CIRCUITSTATE/Mitayi-Pico-RP2040/Export/R0.6/2025-04-27/Renders/Mitayi-Pico-D1-R0.6-PCB-Left-27042025-1.png

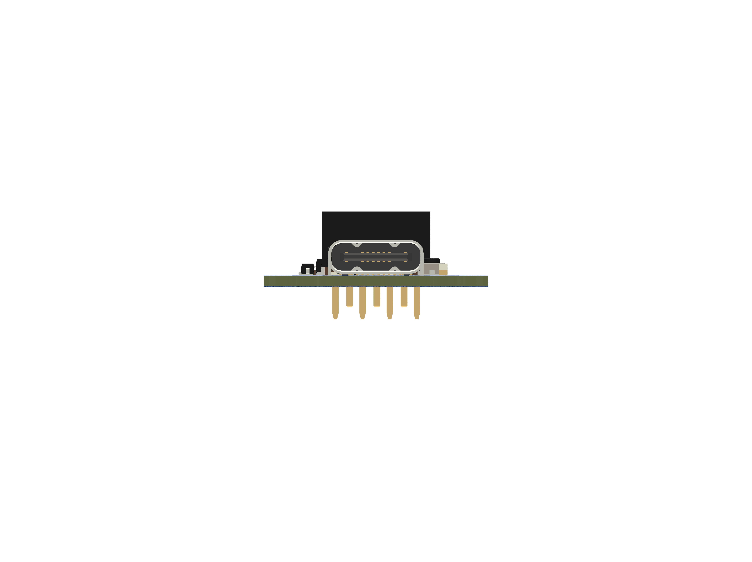
Export/R0.6/2025-04-27/Renders/Mitayi-Pico-D1-R0.6-PCB-Left-27042025-1.png
