CIRCUITSTATE/Mitayi-Pico-RP2040/Revisions/Mitayi-Pico-RP2040-r0.3/Production/PCBWay/[1] 26-08-2022/Mitayi-Pico-RP2040-PCBWay-Order-Details-01.png

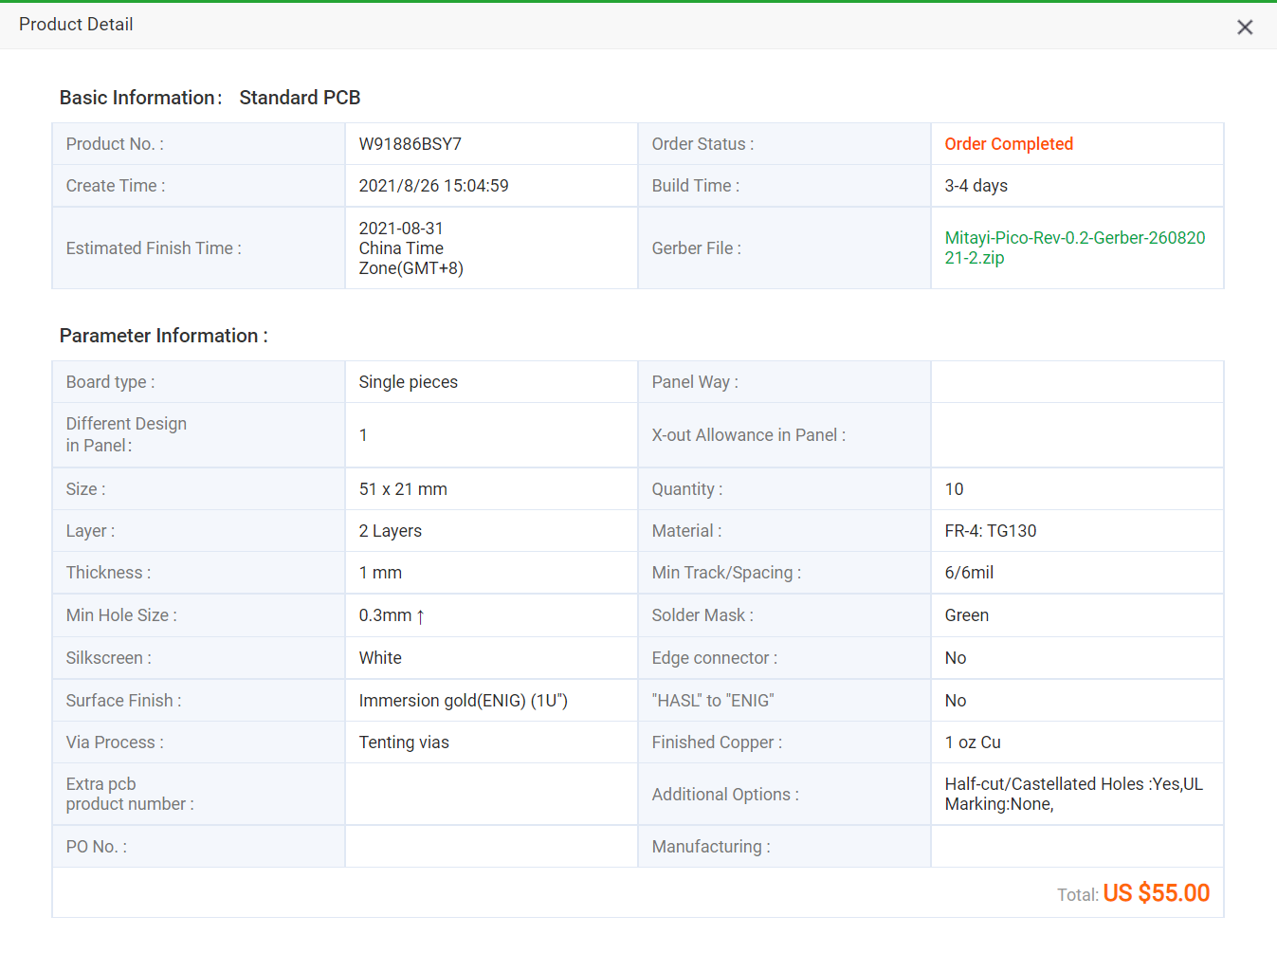
Revisions/Mitayi-Pico-RP2040-r0.3/Production/PCBWay/[1] 26-08-2022/Mitayi-Pico-RP2040-PCBWay-Order-Details-01.png
