CIRCUITSTATE/Mitayi-Pico-RP2040/Revisions/Mitayi-Pico-RP2040-r0.5/Revisions/Mitayi-Pico-RP2040-r0.2/Export/[3] 24-11-2021/Assembly/Mitayi-Pico-RP2040-v0.2-Assembly-Drawing-01_1.png

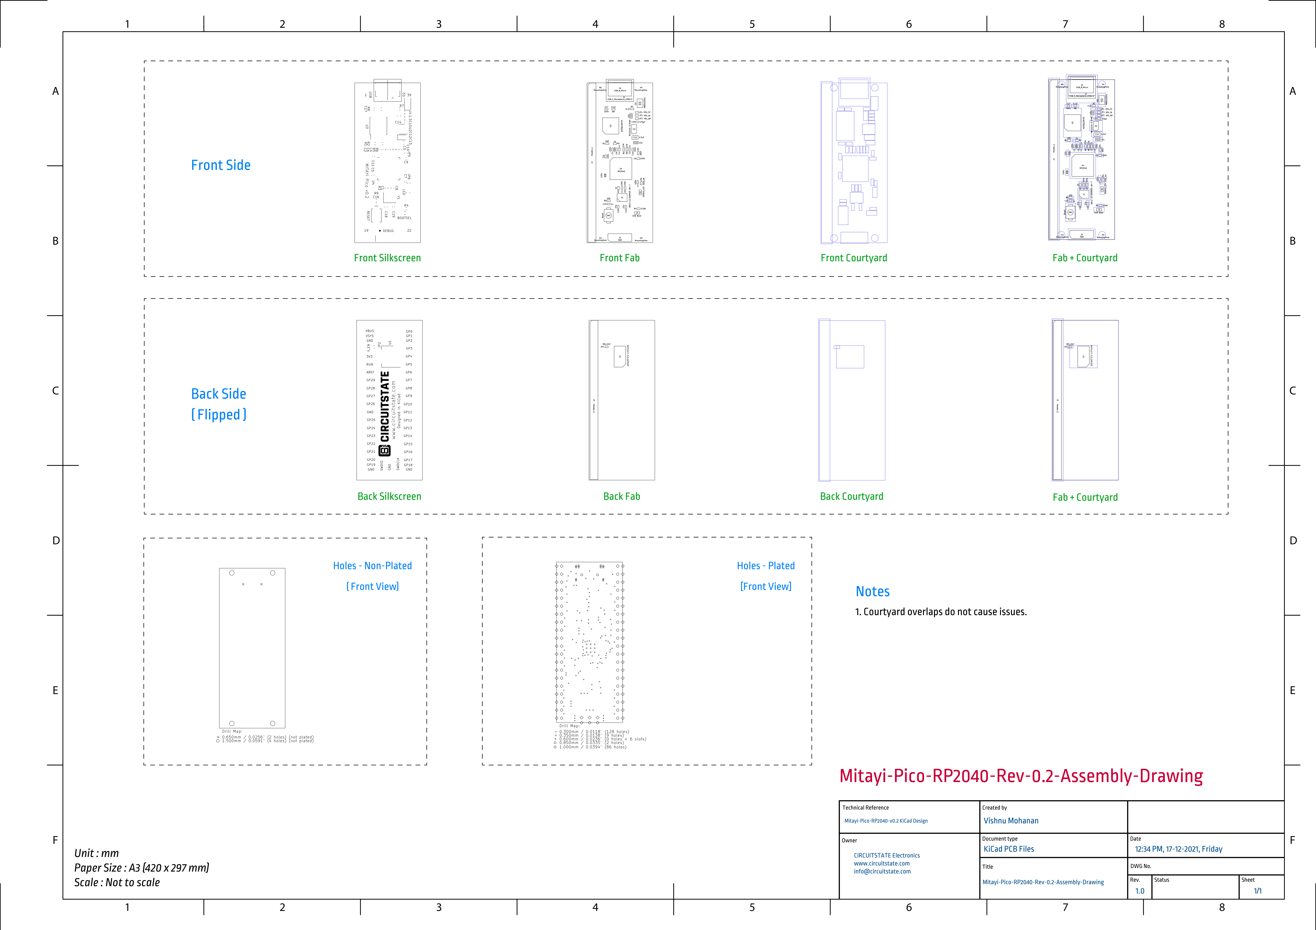
Revisions/Mitayi-Pico-RP2040-r0.5/Revisions/Mitayi-Pico-RP2040-r0.2/Export/[3] 24-11-2021/Assembly/Mitayi-Pico-RP2040-v0.2-Assembly-Drawing-01_1.png
