CIRCUITSTATE/Mitayi-Pico-RP2040/Revisions/Mitayi-Pico-RP2040-r0.4/Export/[6] 23-09-2022/r0.4/Images/Mitayi Pico - PCB.0.4.B.png

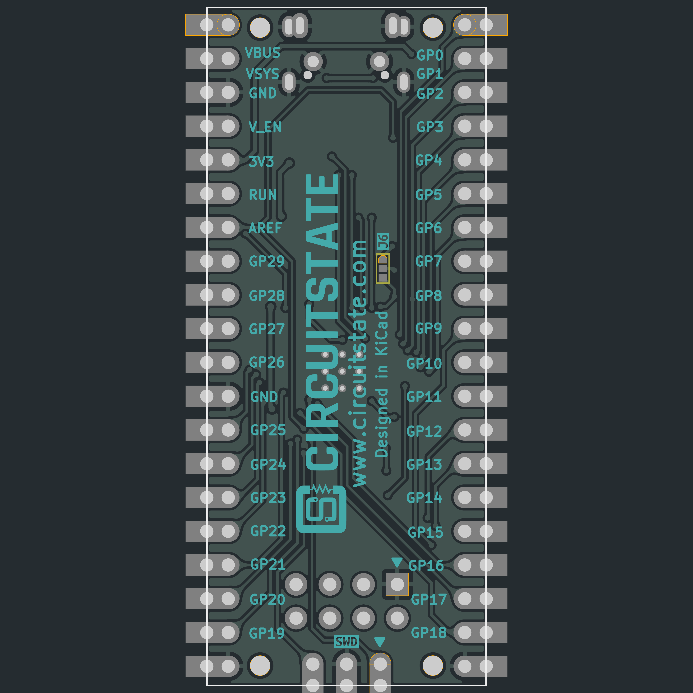
Revisions/Mitayi-Pico-RP2040-r0.4/Export/[6] 23-09-2022/r0.4/Images/Mitayi Pico - PCB.0.4.B.png
