CIRCUITSTATE/Mitayi-Pico-RP2040/Revisions/Mitayi-Pico-RP2040-r0.4/Export/[6] 23-09-2022/r0.4/Images/Mitayi-Pico-RP2040-r0.4-PCB-01-Front-2.png

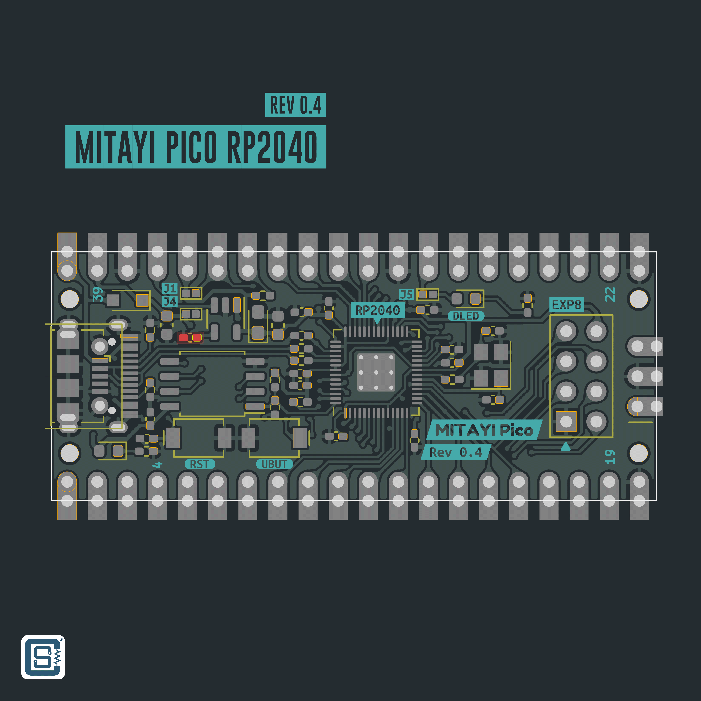
Revisions/Mitayi-Pico-RP2040-r0.4/Export/[6] 23-09-2022/r0.4/Images/Mitayi-Pico-RP2040-r0.4-PCB-01-Front-2.png
