CIRCUITSTATE/Mitayi-Pico-RP2040/Revisions/Mitayi-Pico-RP2040-r0.5/Revisions/Mitayi-Pico-RP2040-r0.2/Export/[3] 24-11-2021/PCB/Mitayi-Pico-RP2040-B_Courtyard.pdf

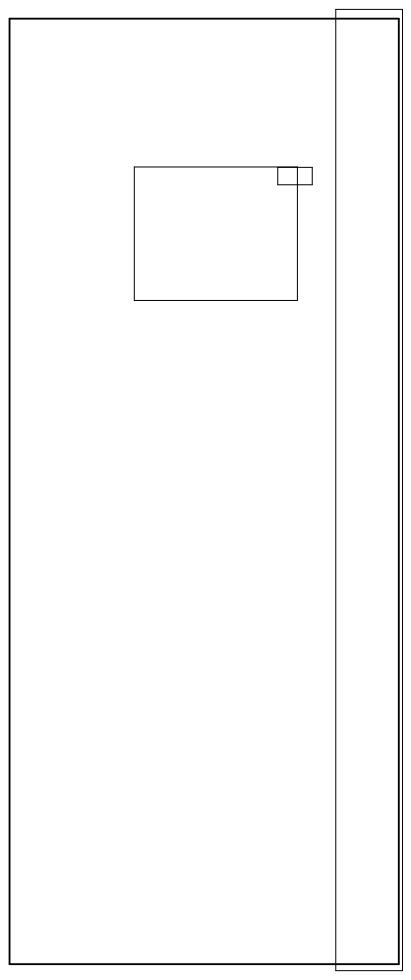
[picture p23: page 1]

Copyright 2021 CIRCUITSTATE Electronics
File: Mitayi-Pico-RP2040.kicad_pcb Sheet: CIRCUITSTATE Electronics Designed by Vishnu Mohanan

Id: 1/1 Title: Mitayi Pico - PCB
