CIRCUITSTATE/Mitayi-Pico-RP2040/Revisions/Mitayi-Pico-RP2040-r0.5/Revisions/Mitayi-Pico-RP2040-r0.2/Export/[3] 24-11-2021/Assembly/Mitayi-Pico-RP2040-v0.2-Assembly-Drawing-01.pdf

## Front Side

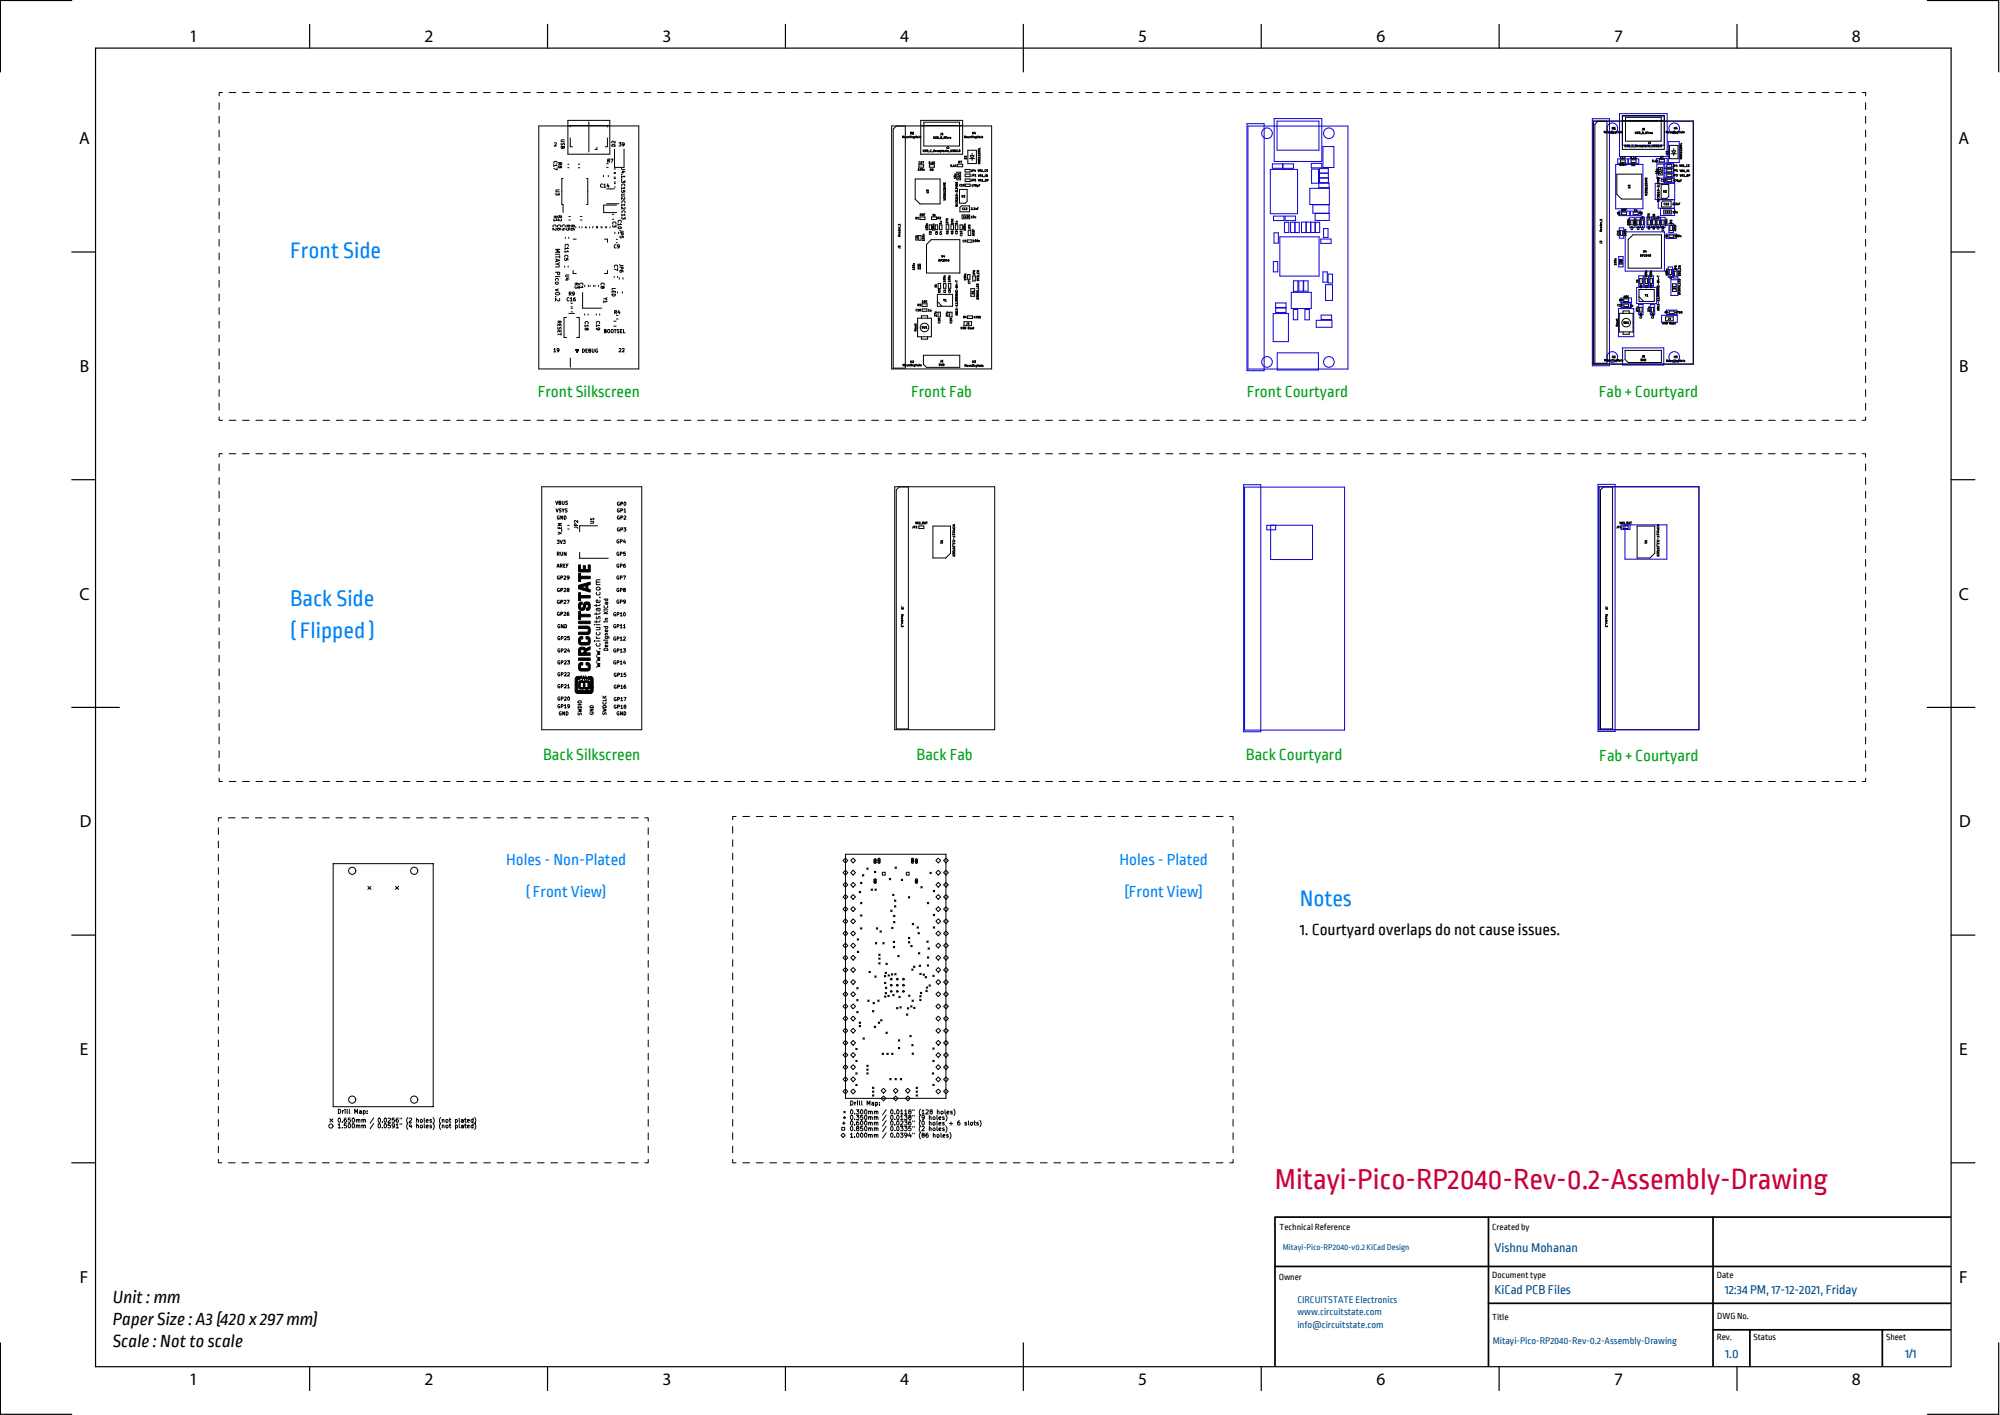
[picture p24: page 1]
Technical Reference; Owner; Created by; Document type; Date; Mitayi-Pico-RP2040-v0.2 KiCad Design; Vishnu Mohanan; 12:34 PM, 17-12-2021, Friday; Front Silkscreen; Back Silkscreen; Holes - Plated; [Front View]; Notes; Back Fab; Back Courtyard; Front Fab; Front Courtyard; Fab + Courtyard; Back Side ( Flipped )

Holes - Non-Plated
( Front View)

1. Courtyard overlaps do not cause issues.

Mitayi-Pico-RP2040-Rev-0.2-Assembly-Drawing

Unit : mm
Paper Size : A3 (420 x 297 mm)
Scale : Not to scale

KiCad PCB Files

CIRCUITSTATE Electronics
www.circuitstate.com
info@circuitstate.com

Title Mitayi-Pico-RP2040-Rev-0.2-Assembly-Drawing | DWG No.

Rev. 1.0 | Status | Sheet 1/1
