CIRCUITSTATE/Mitayi-Pico-RP2040/Export/R0.6/2025-04-27/PCB/Mitayi-Pico-D1-R0.6-Edge_Cuts.pdf

Id: 1/1 Title: Mitayi-Pico-D1
