CIRCUITSTATE/Mitayi-Pico-RP2040/Export/R0.6/2025-04-27/PCB/Mitayi-Pico-D1-R0.6-F_Silkscreen.pdf

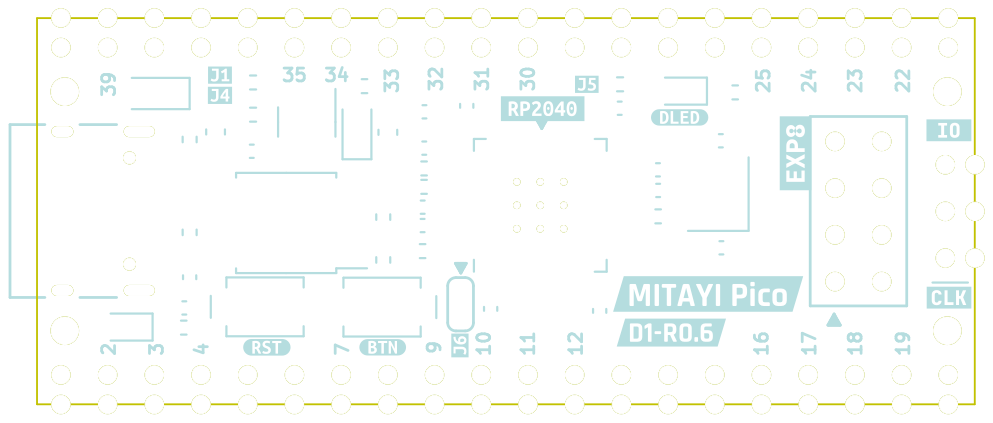
[picture p36: page 1]

Id: 1/1 Title: Mitayi-Pico-D1
