CIRCUITSTATE/Mitayi-Pico-RP2040/Export/R0.6/2025-04-27/PCB/Mitayi-Pico-D1-R0.6-PCB-PDF-All-27042025-1.pdf

D Date: 2025-04-27 KiCad; E.D.A. 9.0.1 Size: A4; Rev: 0.6; File: Mitayi-Pico-D1.kicad_pcb Sheet: CIRCUITSTATE; Electronics; LLP (www.circuitstate.com); Designed; by: Vishnu; Mohanan (@vishnumaiea) Released; under; MIT Open-source; License

Id: 1/1 Title: Mitayi-Pico-D1

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

Id: 1/1 Title: Mitayi-Pico-D1

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

Id: 1/1 Title: Mitayi-Pico-D1

D Date: 2025-04-27 KiCad; E.D.A. 9.0.1 Size: A4; Rev: 0.6; File: Mitayi-Pico-D1.kicad_pcb Sheet: CIRCUITSTATE; Electronics; LLP (www.circuitstate.com); Designed; by: Vishnu; Mohanan (@vishnumaiea) Released; under; MIT Open-source; License OSHW

Id: 1/1 Title: Mitayi-Pico-D1

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

Id: 1/1 Title: Mitayi-Pico-D1

D Date: 2025-04-27 KiCad; E.D.A. 9.0.1 Size: A4; Rev: 0.6; File: Mitayi-Pico-D1.kicad_pcb Sheet: CIRCUITSTATE; Electronics; LLP (www.circuitstate.com); Designed; by: Vishnu; Mohanan (@vishnumaiea) Released; under; MIT Open-source; License GP18 GP5 VSYS GND; GND; AREF; GP13 GP0 VBUS; www.circuitstate.com GP4; RUN; GP23 KiCad; with

Id: 1/1 Title: Mitayi-Pico-D1

Id: 1/1 Title: Mitayi-Pico-D1

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

Id: 1/1 Title: Mitayi-Pico-D1

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

Id: 1/1 Title: Mitayi-Pico-D1


Id: 1/1 Title: Mitayi-Pico-D1

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

Id: 1/1 Title: Mitayi-Pico-D1

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

Id: 1/1 Title: Mitayi-Pico-D1

D Date: 2025-04-27 KiCad; E.D.A. 9.0.1 Size: A4; Rev: 0.6; File: Mitayi-Pico-D1.kicad_pcb Sheet: CIRCUITSTATE; Electronics; LLP (www.circuitstate.com); Designed; by: Vishnu; Mohanan (@vishnumaiea) Released; under; MIT Open-source; License ²³³⁵

Id: 1/1 Title: Mitayi-Pico-D1

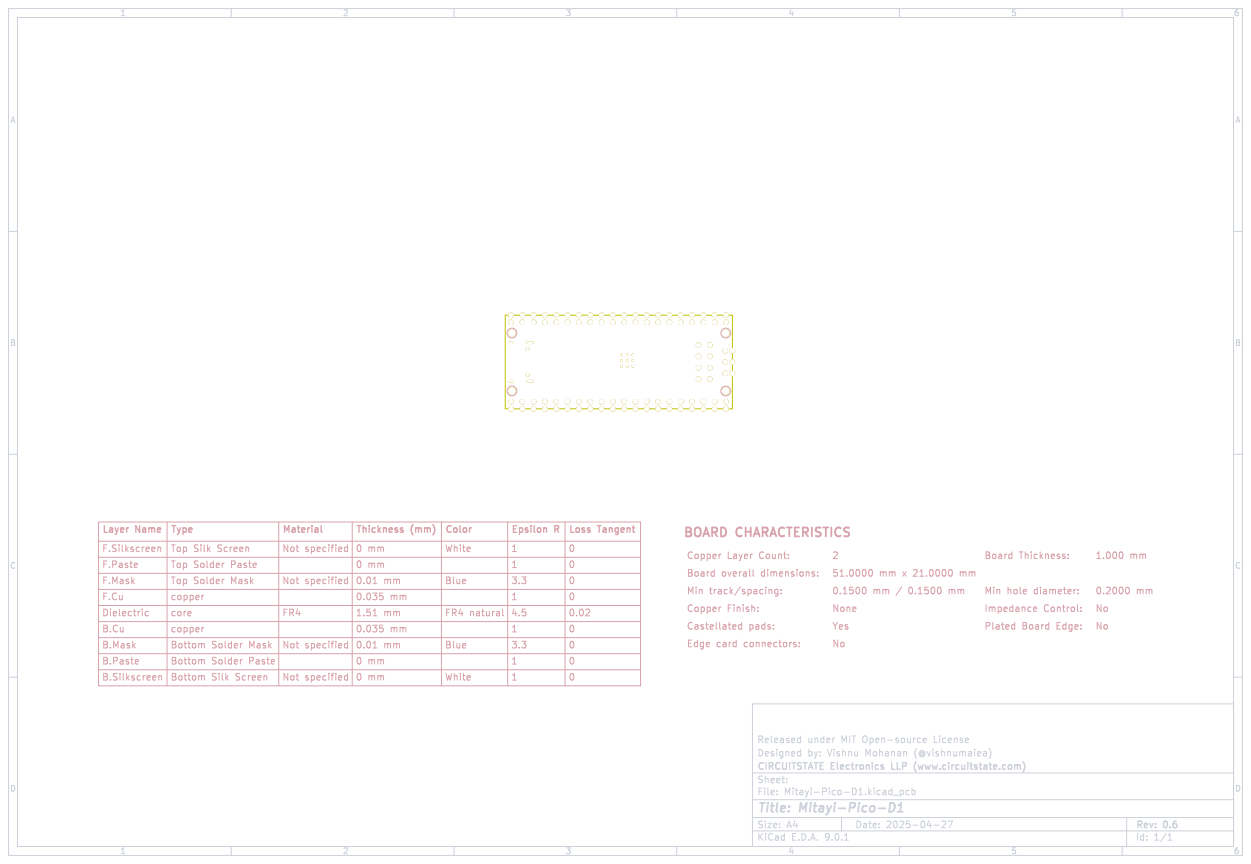
[picture p37: page 14]
D Date: 2025-04-27 KiCad; E.D.A. 9.0.1 Size: A4; Rev: 0.6; File: Mitayi-Pico-D1.kicad_pcb Sheet: CIRCUITSTATE; Electronics; LLP (www.circuitstate.com); Designed; by: Vishnu; Mohanan (@vishnumaiea) Released; under; MIT Open-source; License; 0.02 Top Solder; Paste B.Mask; Copper; Finish: Top Solder; Mask; No Not specified; Yes No; 0 F.Silkscreen; None; Min; hole diameter: 0.035 mm; Top Silk; Screen; Layer Name; Min track/spacing: 0 mm; Edge card; connectors:; Plated; Board; Edge: Dielectric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

F.Mask | | | 0 mm | Color 0 mm | 1

copper | Not specified | | Blue F.Paste | 1 | Loss Tangent 0 Type 0

Thickness (mm) | White

1 B.Silkscreen 3.3

Not specified | 0 mm | | 1 | 0

Id: 1/1 Title: Mitayi-Pico-D1

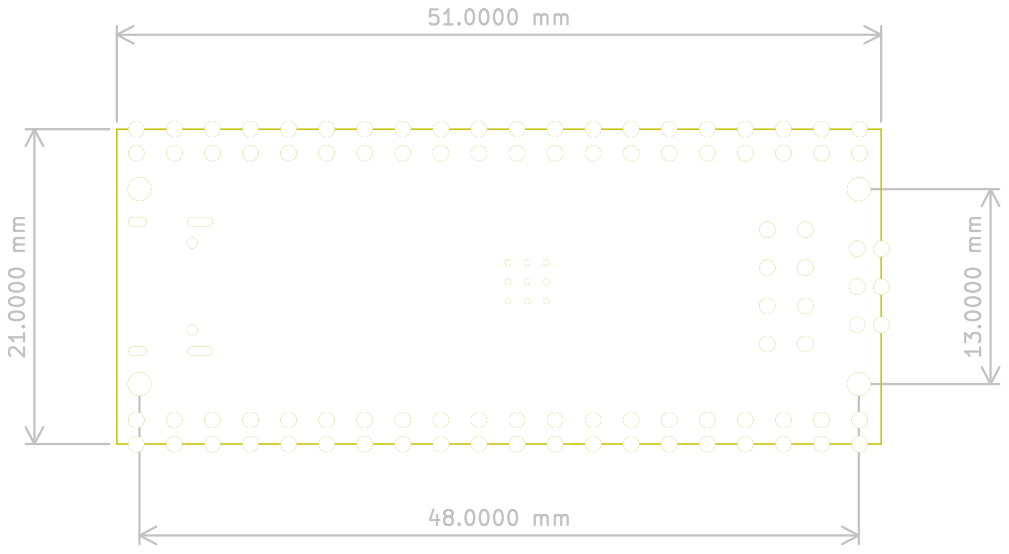
[picture p38: page 15]
D Date: 2025-04-27 KiCad; E.D.A. 9.0.1 Size: A4; Rev: 0.6; File: Mitayi-Pico-D1.kicad_pcb Sheet: CIRCUITSTATE; Electronics; LLP (www.circuitstate.com); Designed; by: Vishnu; Mohanan (@vishnumaiea) Released; under; MIT Open-source; License ¹³.0000 mm 21.0000 mm

Id: 1/1 Title: Mitayi-Pico-D1
