CIRCUITSTATE/Mitayi-Pico-RP2040/Export/R0.6/2025-04-27/SCH/Mitayi-Pico-D1-R0.6-SCH-27042025-1.pdf

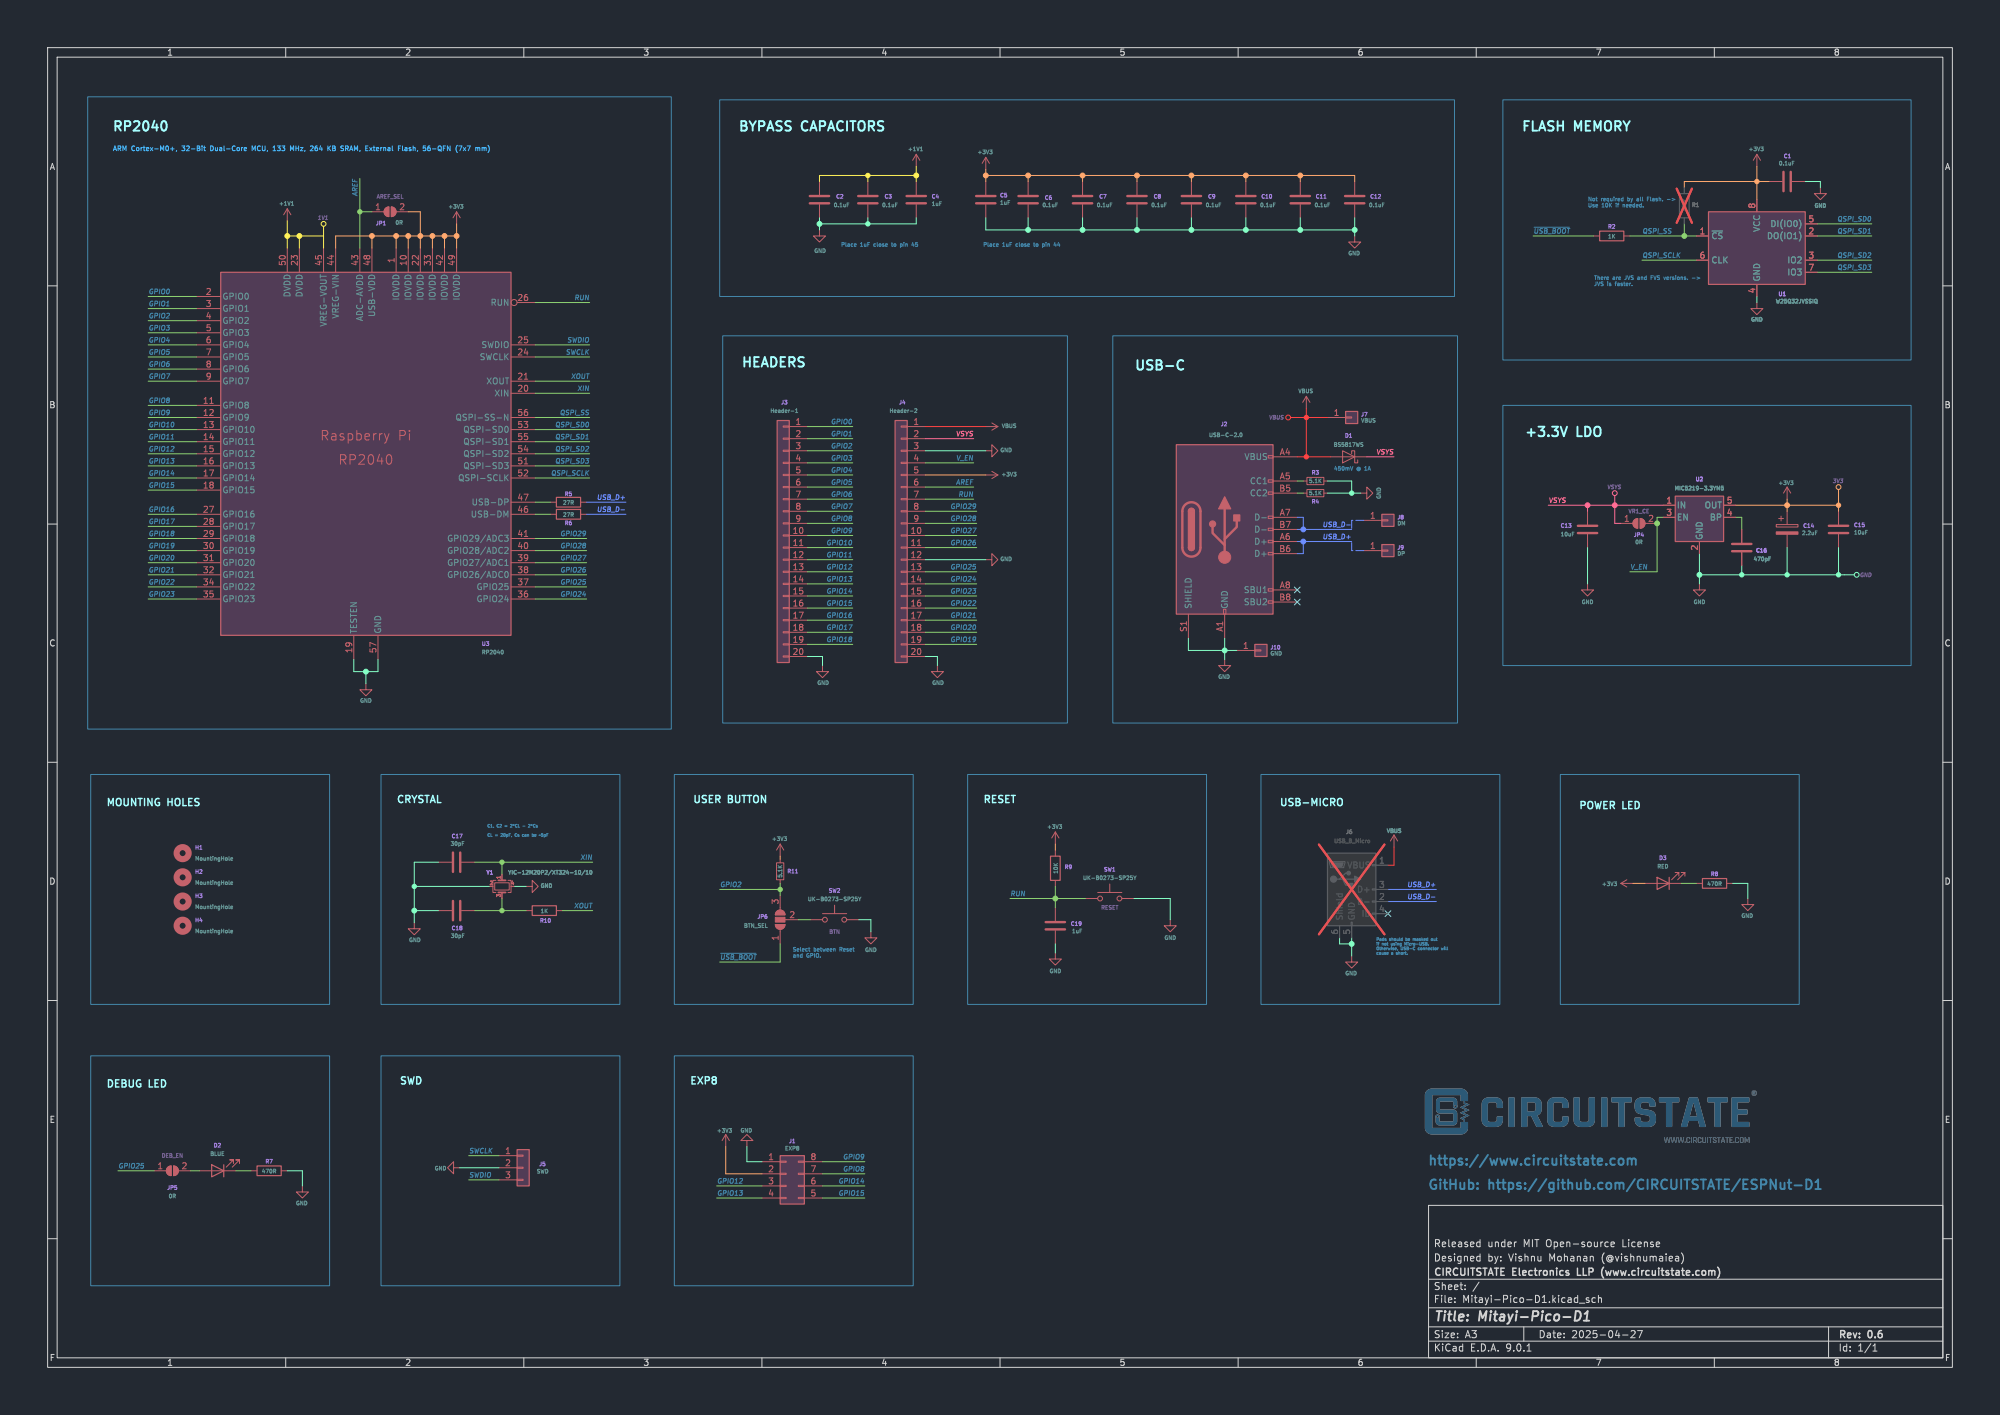
[picture p39: page 1]

1 IOVDD 10 IOVDD 22 IOVDD 33 IOVDD 42 IOVDD 49 RUN 26 SWDIO 25 SWCLK 24 XOUT 21 XIN 20 QSPI-SS-N 56 QSPI-SD0 53 QSPI-SD1 55 QSPI-SD2 54 QSPI-SD3 51 QSPI-SCLK 52 USB-DP 47 USB-DM 46 GPIO29/ADC3 41 GPIO28/ADC2 40 GPIO27/ADC1 39 GPIO26/ADC0 38 GPIO25 37 GPIO24 36

https://www.circuitstate.com
GitHub: https://github.com/CIRCUITSTATE/ESPNut-D1

Id: 1/1 Title: Mitayi-Pico-D1
