CIRCUITSTATE/Mitayi-Pico-RP2040/Revisions/Mitayi-Pico-RP2040-r0.5/Revisions/Mitayi-Pico-RP2040-r0.2/Export/[3] 24-11-2021/PCB/Mitayi-PCB-Image-01.pdf

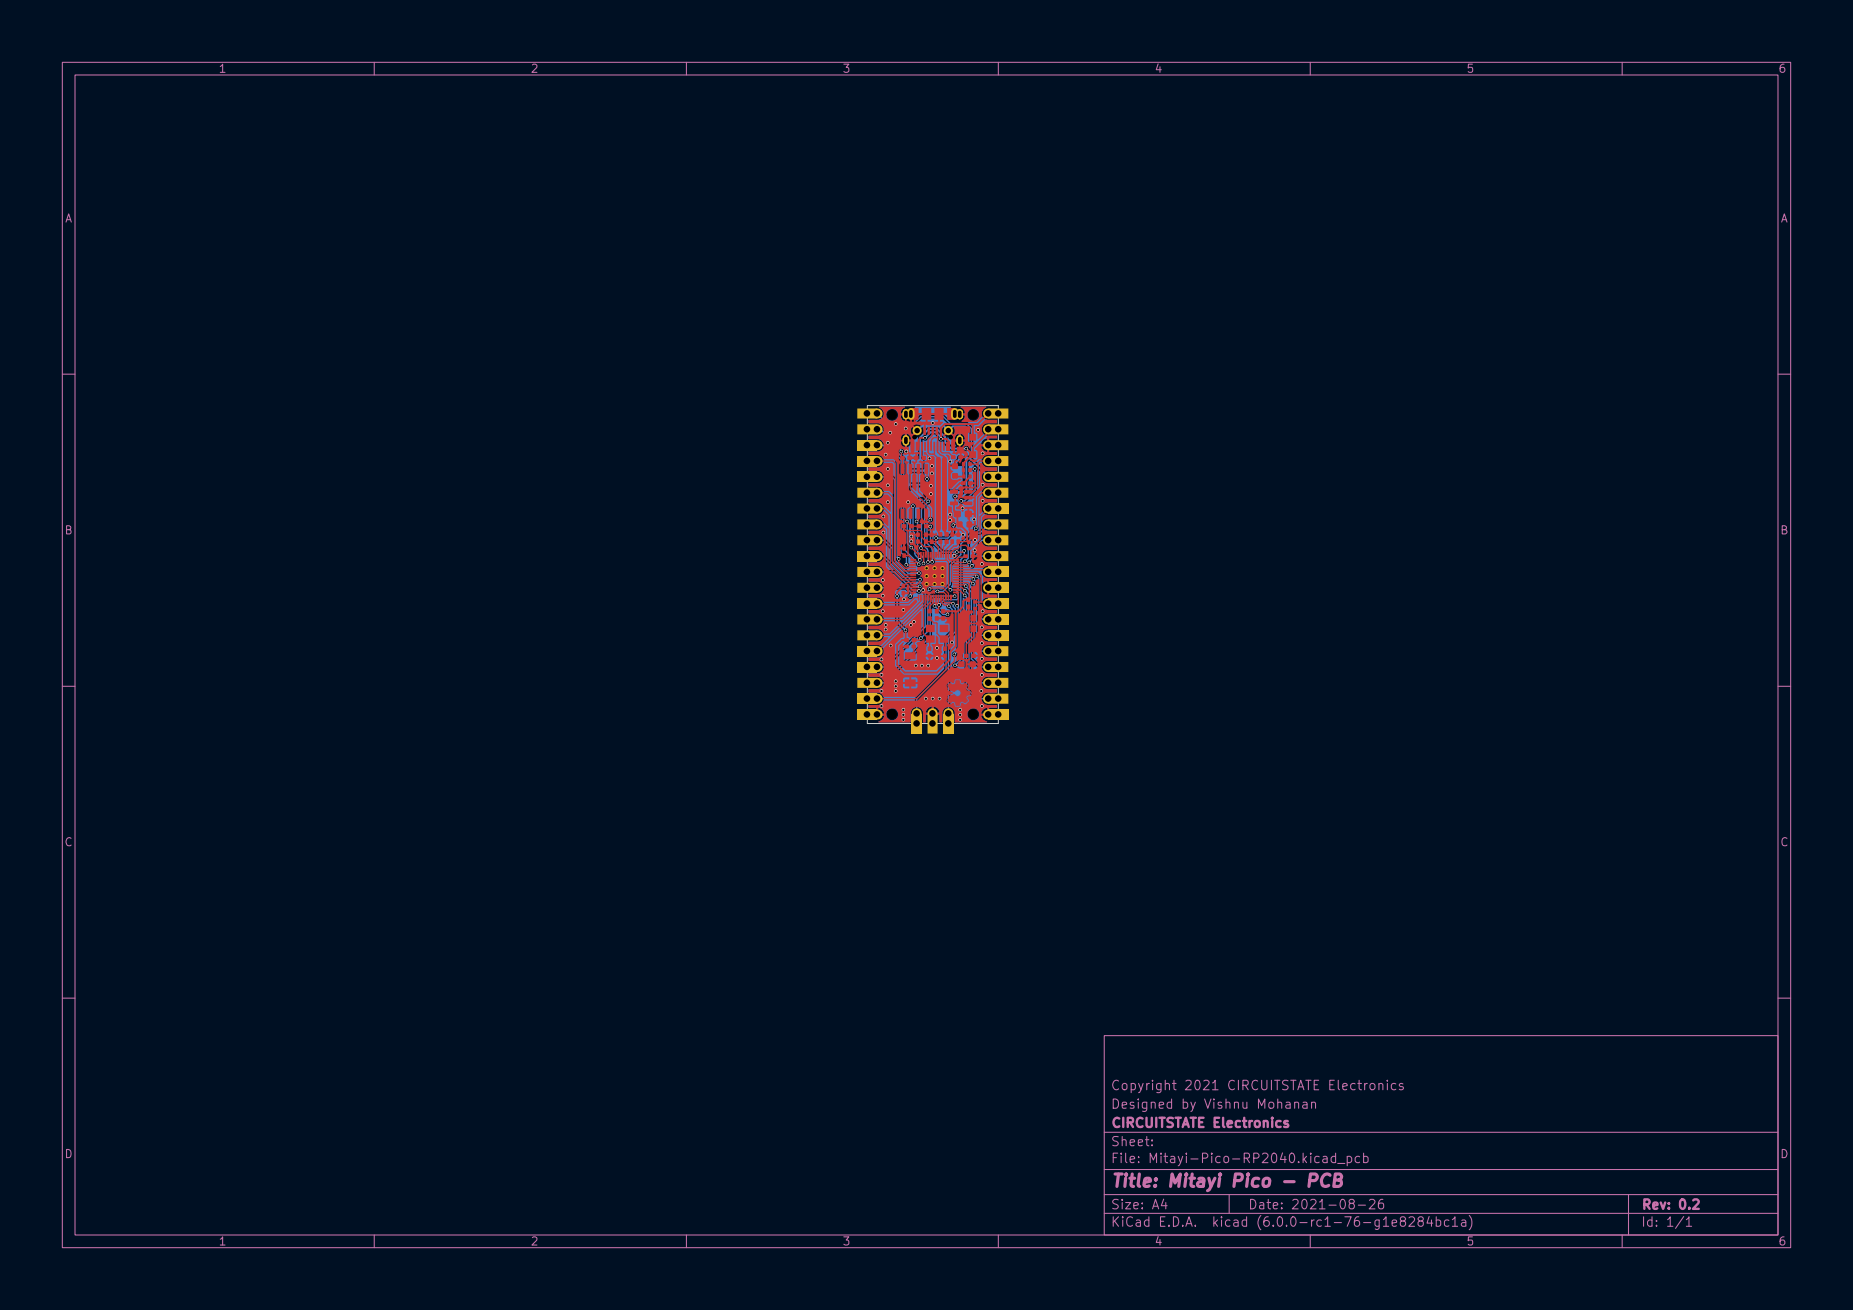
[picture p40: page 1]
